pedrojteix/Smartgrow/hardware/kicad/SGRW_Controller/SGRW_Controller.kicad_sch

## KiCad design hardware/kicad/SGRW_Controller/SGRW_Controller.kicad_sch (2026-08-07)

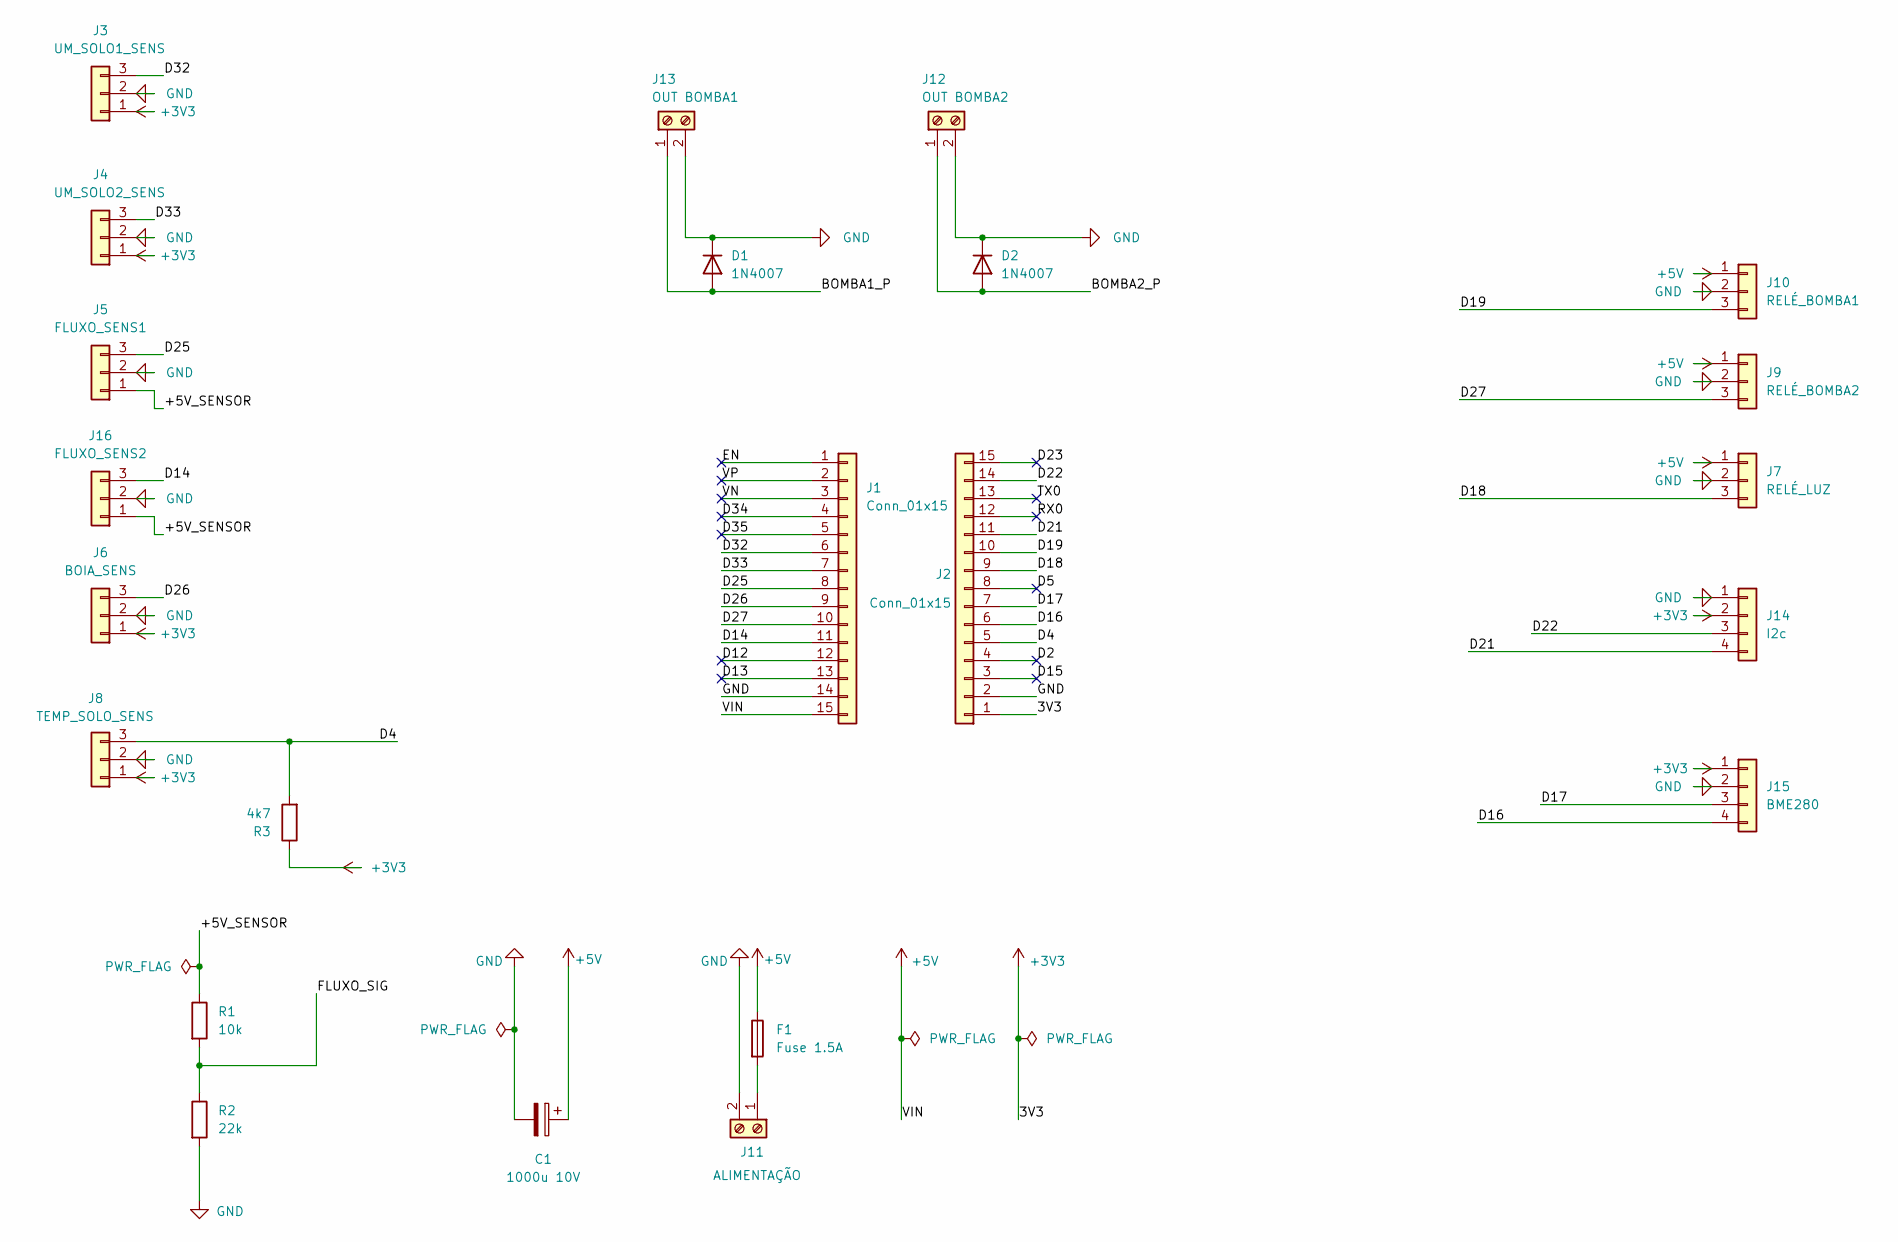
[picture p3: schematic SGRW_Controller.kicad_sch]

Parts:
C1: 1000u 10V
D1, D2: 1N4007; D_DO-41_SOD81_P10.16mm_Horizontal
F1: Fuse 1.5A
J1, J2: Conn_01x15
J3: UM_SOLO1_SENS
J4: UM_SOLO2_SENS
J5: FLUXO_SENS1
J6: BOIA_SENS
J7: RELÉ_LUZ
J8: TEMP_SOLO_SENS
J9: RELÉ_BOMBA2
J10: RELÉ_BOMBA1
J11: ALIMENTAÇÃO
J12: OUT BOMBA2
J13: OUT BOMBA1
J14: I2c
J15: BME280
J16: FLUXO_SENS2
R1: 10k
R2: 22k
R3: 4k7

Connections:
+3V3: J2.1, J3.1, J4.1, J6.1, J8.1, J14.2, J15.1, R3.1
+5V: C1.1, F1.1, J1.15, J7.1, J9.1, J10.1
+5V_SENSOR: J5.1, J16.1, R1.1
BOMBA1_P: D1.2 (A), J13.1
BOMBA2_P: D2.2 (A), J12.1
D2: J2.4
D4: J2.5, J8.3, R3.2
D5: J2.8
D12: J1.12
D13: J1.13
D14: J1.11, J16.3
D15: J2.3
D16: J2.6, J15.4
D17: J2.7, J15.3
D18: J2.9, J7.3
D19: J2.10, J10.3
D21: J2.11, J14.4
D22: J2.14, J14.3
D23: J2.15
D25: J1.8, J5.3
D26: J1.9, J6.3
D27: J1.10, J9.3
D32: J1.6, J3.3
D33: J1.7, J4.3
D34: J1.4
D35: J1.5
EN: J1.1
FLUXO_SIG: R1.2, R2.1
GND: C1.2, D1.1 (K), D2.1 (K), J1.14, J2.2, J3.2, J4.2, J5.2, J6.2, J7.2, J8.2, J9.2, J10.2, J11.2, J12.2, J13.2, J14.1, J15.2, J16.2, R2.2
unnamed: F1.2, J11.1
RX0: J2.12
TX0: J2.13
VN: J1.3
VP: J1.2
